mrhunsaker/ScreenReaderTactileGraphics/Pdf/PowerPoint Online.bpx.pdf

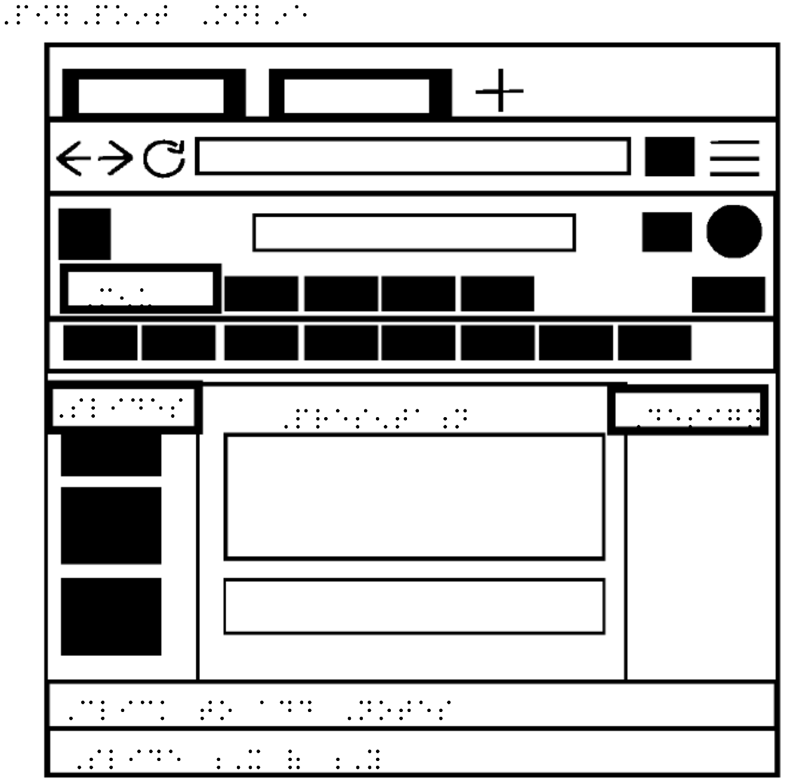
[picture p12: page 1]

,P[],PO9T ,ONL9E

,M5U

,PRES5TA;N ,SLIDES

,CLICK TO ADD ,NOTES

,SLIDE ;,X ( ;,Y

,DESIGN
