mrhunsaker/ScreenReaderTactileGraphics/Pdf/WebsiteHeadings.bpx.pdf

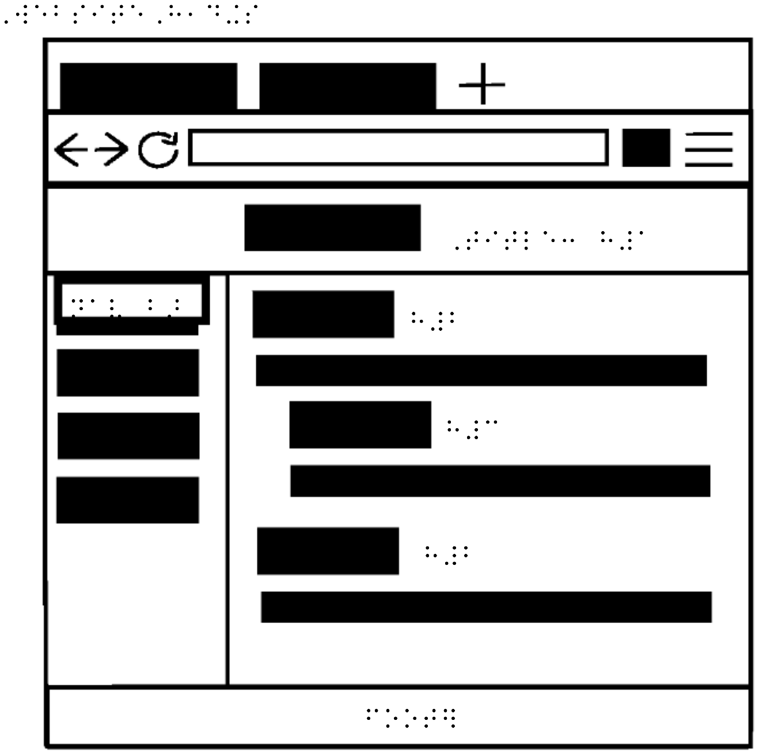
[picture p13: page 1]

,WEBSITE,H1D+S

,TITLE3 H#A

NAV B> | H#B

H#C

H#B

FOOT]
