mrhunsaker/ScreenReaderTactileGraphics/Pdf/Word Online.bpx.pdf

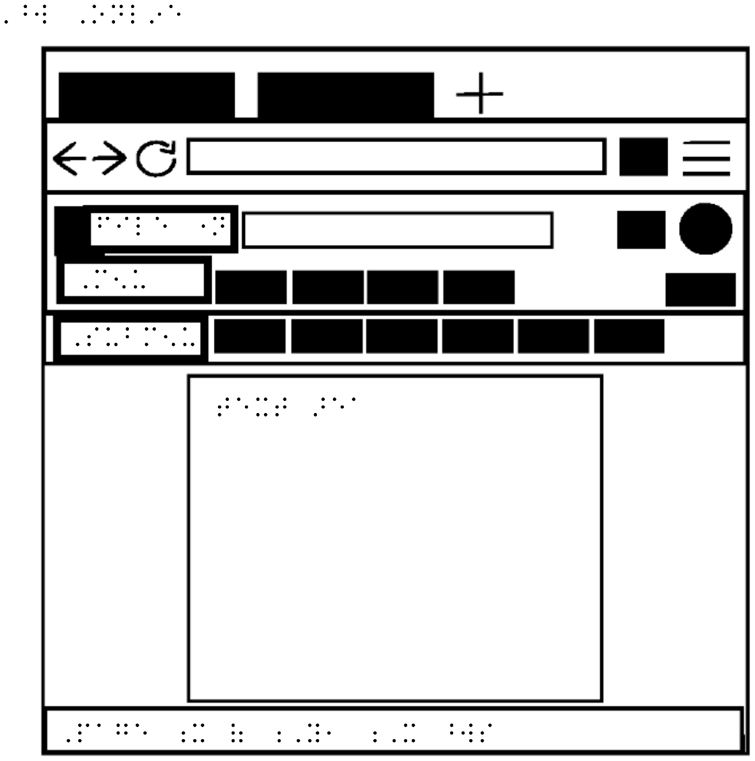
[picture p14: page 1]

,^W ,ONL9E

,M5U

,PAGE ;X ( ;,Y1 ;,X ^WS

FILE "N

,SUBM5U

TEXT >EA
